galjonsfigur/led-pedestal/media/connected_rev1.jpg

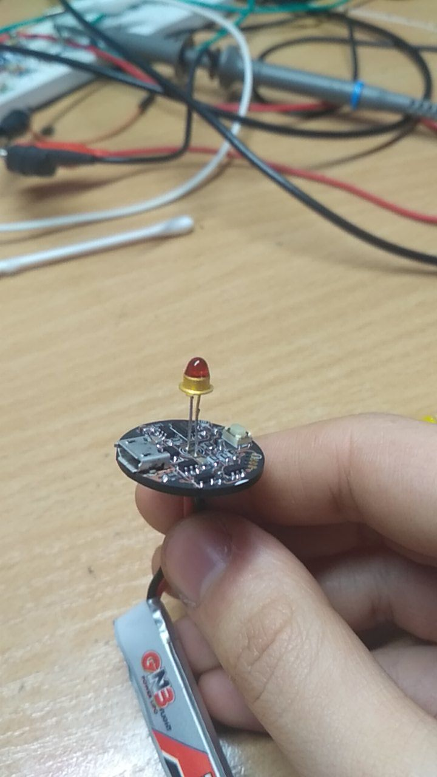
media/connected_rev1.jpg
