galjonsfigur/led-pedestal/media/prototypes.jpg

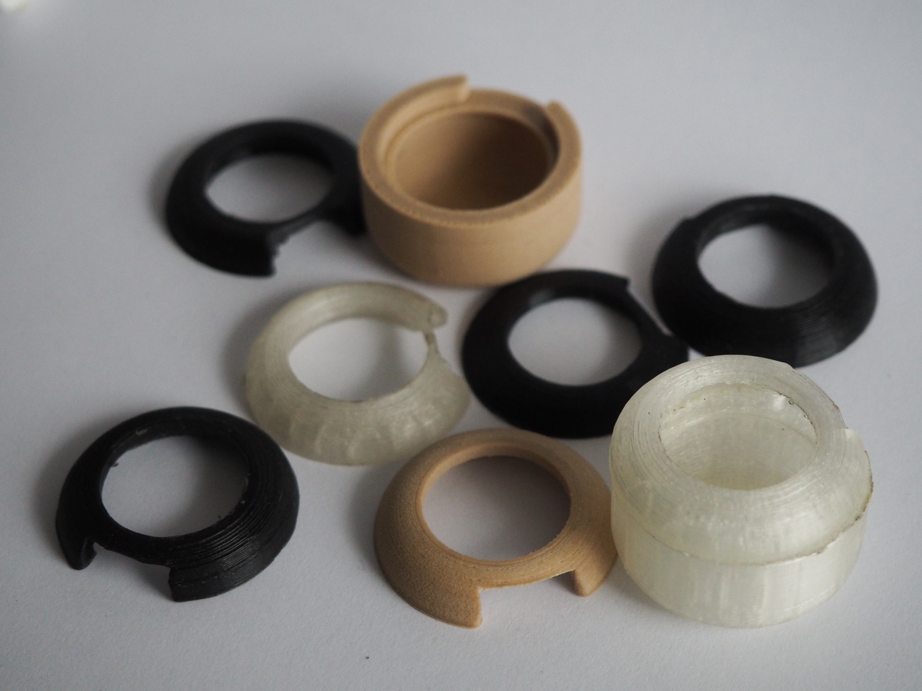
media/prototypes.jpg
