galjonsfigur/led-pedestal/media/soldered_rev1.jpg

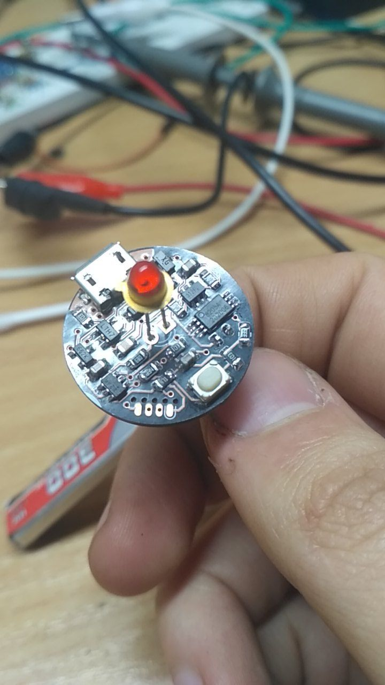
media/soldered_rev1.jpg
